jmysu/mBusCH55x/firmware/cdcCMDs559.MCS51/extra_script.py

''' custom script for platformio '''

from os.path import join
from SCons.Script import DefaultEnvironment

env = DefaultEnvironment()

print ("Custom extra_script launching...")
#
#1. warning 126 : unreachable code.
#2. warning 59 : conditional flow changed by optimizer.
#3. linker flag : --xram-loc
env.Append(
    CFLAGS = [
        "--disable-warning", 110,
        "--disable-warning", 126,
        "--disable-warning", 59
        ],
    LINKFLAGS = [
        "--xram-size", 0x1800,
        "--xram-loc", 0x0000,
        "--model-large",
        "--stack-auto",
        ]
    )
print("LINKFLAGS:"+env["LINKFLAGS"])

# In-line command with arguments
#env.Replace(
#    UPLOADCMD="executable -arg1 -arg2 $SOURCE"
#)
